brlnoble/RIPT_Capstone/CAD Designs/finger.stl

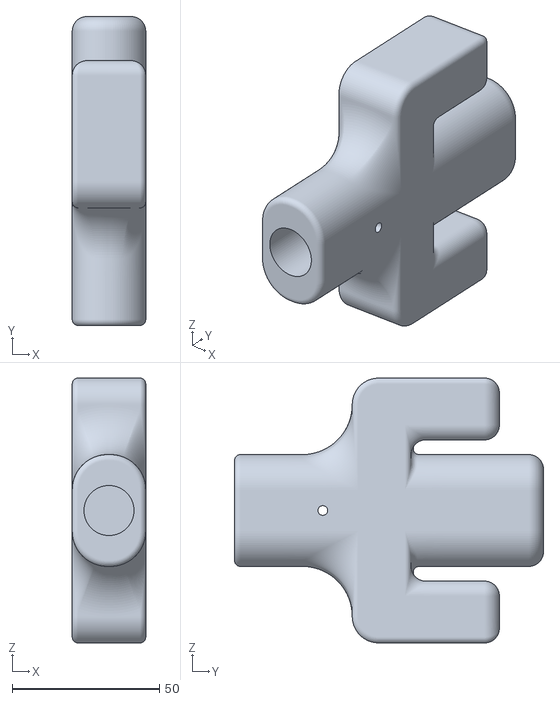
[picture p20: CAD file, 2023-04-15]
CAD Designs/finger.stl
25.0 x 105.0 x 90.0
