brlnoble/RIPT_Capstone/CAD Designs/separator_plate_alternate.stl

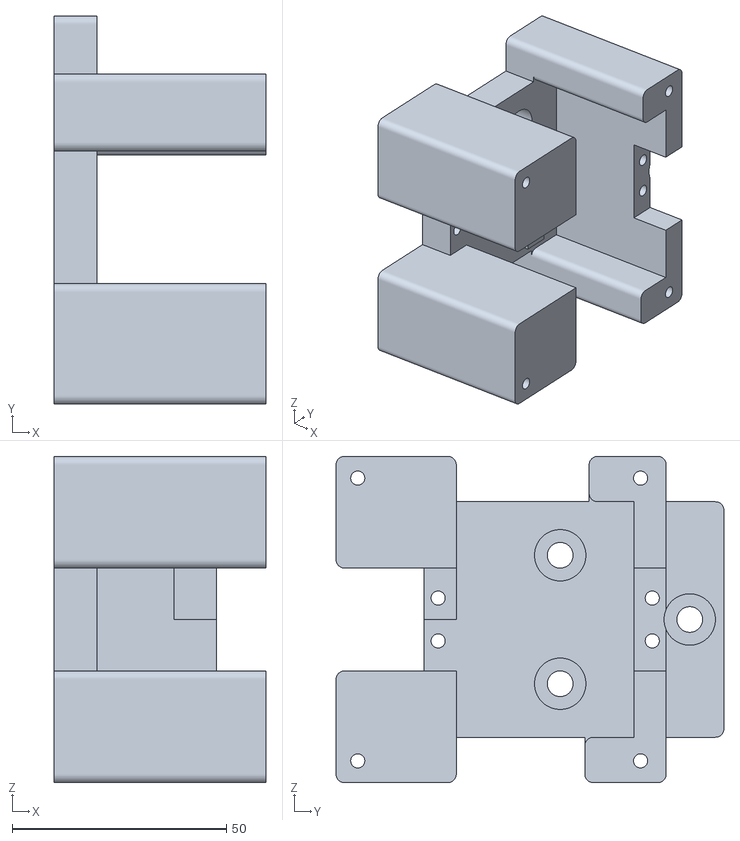
[picture p21: CAD file, 2023-04-15]
CAD Designs/separator_plate_alternate.stl
49.5 x 90.6 x 76.2
