brlnoble/RIPT_Capstone/CAD Designs/servo_horz_plate.stl

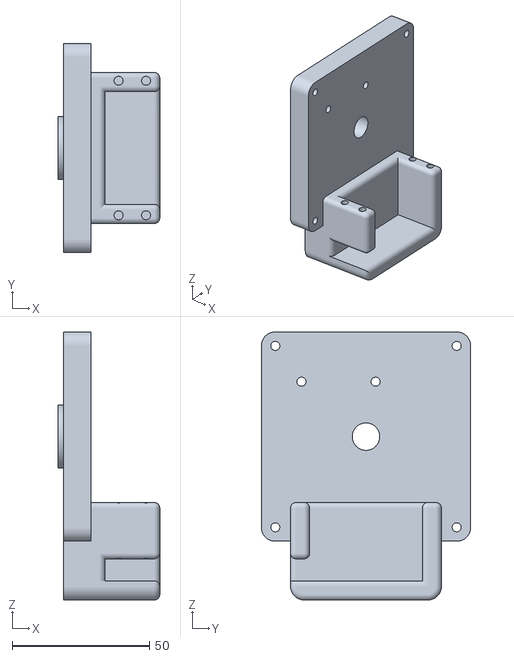
[picture p22: CAD file, 2023-04-15]
CAD Designs/servo_horz_plate.stl
37.0 x 76.2 x 97.6
