brlnoble/RIPT_Capstone/CAD Designs/servo_pressfit_plate.stl

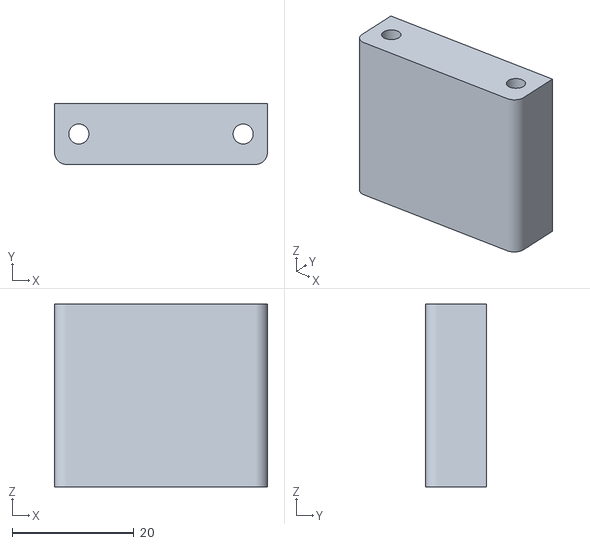
[picture p23: CAD file, 2023-04-15]
CAD Designs/servo_pressfit_plate.stl
35.0 x 10.0 x 30.0
