brlnoble/RIPT_Capstone/CAD Designs/stick_mount.stl

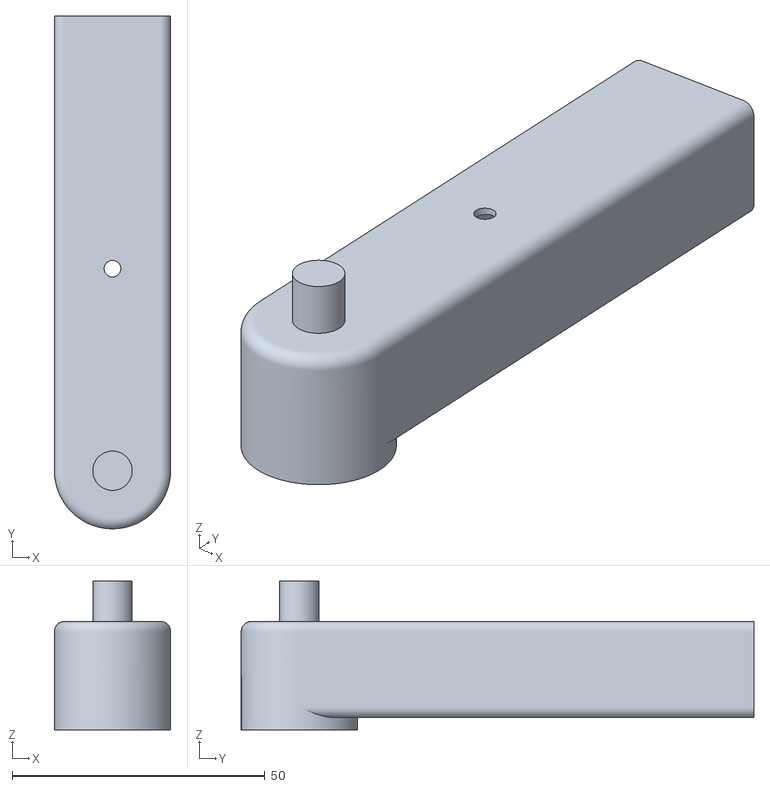
[picture p24: CAD file, 2023-04-15]
CAD Designs/stick_mount.stl
23.0 x 101.5 x 29.5
