brlnoble/RIPT_Capstone/CAD Designs/Slider Top 2.stl

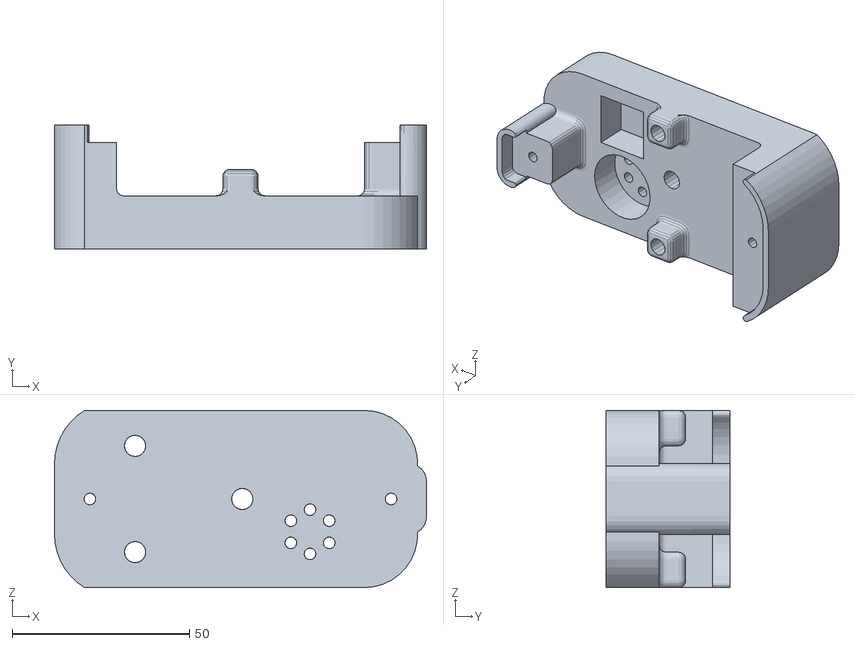
[picture p25: CAD file, 2023-04-15]
CAD Designs/Slider Top 2.stl
105.0 x 35.0 x 50.0
