brlnoble/RIPT_Capstone/MotorMove.py

m1_1 = 1
m1_2 = 2
m2_1 = 3
m2_2 = 4
m1_rx = 5
m1_ry = 6
m2_rx = 7
m2_ry = 8

def MotorMove(x1,x2,y1,y2,type):
    dx=x2-x1
    dy=y2-y1

    xdir = (abs(dx)-dx)/abs(2*dx)
    ydir = (abs(dy)-dy)/abs(2*dy)

def hook():
