brlnoble/RIPT_Capstone/MotorMovementTest.py

import RPi.GPIO as GPIO #for IO control
from time import sleep, perf_counter #for delay functionality
import PySimpleGUI as sg #for simple interface
import random #for random positions

#~~~~~~~~~~~~~~~~~~~~~~~~~~~~~~~~~~~~~~~~~~~~~~~~~~~~~~~~~~~~~~~~~~~~~~~~~~~~~~~~~~~~~~~~~~~~~~~~~
#~~~~~~~~~~~~~~~~~~~~~~~~~~~~~~~~~~~~~~~~~~~~~ Setup ~~~~~~~~~~~~~~~~~~~~~~~~~~~~~~~~~~~~~~~~~~~~~

#Define the stepper motor pins
dirPin1 = 21 #direction pin for motor 1
stepPin1 = 20 #pulse pin for motor 1

dirPin2 = 6 #direction pin for motor 2
stepPin2 = 5 #pulse pin for motor 2

#Define the zeroing pins
zeroPinX = 23
zeroPinY = 24

#Parameters of the motors
speed_max_default =  150e3 #delay between pulses (200k Hz default)
speed_min_default = 75e3
m_delay = 0.5 #delay between movements
m_steps = 1600 #steps per rotation (1/8 microstep)
m_diameter = 1.215 #diameter of the motor gear in cm

#Location tracking
x_location = 0
y_location = 0

#Setup the GPIO pins
GPIO.setmode(GPIO.BCM)

GPIO.setup(dirPin1,GPIO.OUT)
GPIO.setup(stepPin1,GPIO.OUT)
GPIO.setup(dirPin2,GPIO.OUT)
GPIO.setup(stepPin2,GPIO.OUT)

GPIO.setup(zeroPinX,GPIO.IN)
GPIO.setup(zeroPinY,GPIO.OUT)

#Define clockwise and counter clockwise for readability
cw = GPIO.HIGH
ccw = GPIO.LOW

#~~~~~~~~~~~~~~~~~~~~~~~~~~~~~~~~~~~~~~~~~~~~~~~~~~~~~~~~~~~~~~~~~~~~~~~~~~~~~~~~~~~~~~~~~~~~~~~~~
#~~~~~~~~~~~~~~~~~~~~~~~~~~~~~~~~~~~~~~~~~~~ Functions ~~~~~~~~~~~~~~~~~~~~~~~~~~~~~~~~~~~~~~~~~~~

#~~~~~ Convert cm to steps ~~~~~
def Dist_to_Steps(distance):
    return int( (distance / (3.14156 * m_diameter)) * m_steps) #return the number of steps as an integer

#~~~~~ Convert steps to cm ~~~~~
def Steps_to_Dist(steps):
    return (steps / m_steps) * (3.14156 * m_diameter)
    
#~~~~~ Move motors a given number of steps ~~~~~
def Move_Motors(steps,speed_max,speed_min):
    #start_time = perf_counter()
    
    #Accelerate over one rotation if steps and max/min speeds set
    if steps > 1600 and speed_max != speed_min:
        
        accel_step = (speed_max - speed_min)/1600 #Frequency increase per step
        
        for accel in range(0,1600):
            
            accel_speed = 1 / (accel_step*accel + speed_min) #New speed
            
            GPIO.output(stepPin1,GPIO.HIGH)
            GPIO.output(stepPin2,GPIO.HIGH)
            sleep(accel_speed)
            GPIO.output(stepPin1,GPIO.LOW)
            GPIO.output(stepPin2,GPIO.LOW)
            sleep(accel_speed)
            
        #Correct steps and speed for acceleration        
        steps -= 1600
        speed = 1 / speed_max #convert frequency to seconds

    #Move at minimum speed otherwise
    else:
        speed = 1 / speed_min #convert frequency to seconds
    
    #Move the motor in the specified direction for the specified number of steps
    for step in range(steps):
        GPIO.output(stepPin1,GPIO.HIGH)
        GPIO.output(stepPin2,GPIO.HIGH)
        sleep(speed)
        GPIO.output(stepPin1,GPIO.LOW)
        GPIO.output(stepPin2,GPIO.LOW)
        sleep(speed)

#~~~~~ Change motor direction ~~~~~
def Motor_Direction(direction):
    #Change motor direction as specified
    if direction == "up":
        GPIO.output(dirPin1,ccw)
        GPIO.output(dirPin2,cw)
    elif direction == "down":
        GPIO.output(dirPin1,cw)
        GPIO.output(dirPin2,ccw)
    elif direction == "left":
        GPIO.output(dirPin1,ccw)
        GPIO.output(dirPin2,ccw)
    elif direction == "right":
        GPIO.output(dirPin1,cw)
        GPIO.output(dirPin2,cw)

#~~~~~ Movement based on direction and distance ~~~~~
def Move_Distance(direction,distance,x_pos,y_pos):
    start_time = perf_counter()
    #Change motor direction as specified
    Motor_Direction(direction)

    steps_to_move = Dist_to_Steps(distance) #number of steps to move
    dist_to_move = Steps_to_Dist(steps_to_move) #actual distance moved after rounding
    dist_to_move = distance

    #Calculate new position
    if direction == "up":
        y_pos += dist_to_move
        
        #Set the speed for movement
        speed_max = speed_max_default
        speed_min = speed_min_default
        
    elif direction == "down":
        y_pos -= dist_to_move
        
        #Set the speed for movement
        speed_max = speed_max_default
        speed_min = speed_min_default
        
    elif direction == "left":
        x_pos -= dist_to_move
        
        #Set the speed for movement
        speed_max = speed_max_default/2
        speed_min = speed_min_default/2
        
    elif direction == "right":
        x_pos += dist_to_move
        
        #Set the speed for movement
        speed_max = speed_max_default/2
        speed_min = speed_min_default/2

    #Move the motors into position
    if distance != 0:
        Move_Motors(steps_to_move,speed_max,speed_min)
        
        print("\tSteps: " + str(steps_to_move))
        print("\tDist: " + str(dist_to_move))
        print("\tAcc: " + str(100 * (dist_to_move - distance) / distance) + "%")

    end_time = perf_counter()
    print("\tTotal Time: " + str(end_time - start_time) )
    return (x_pos, y_pos) #Return the new X,Y position

#Move to a specific position
def Move_To(x_move,y_move,x_curr,y_curr):
    #Make sure values are valid first
    if x_move <= 12.0 and x_move >= 0.0 and y_move <= 45.0 and y_move >= 0.0:
        
        #Calculate relative movements to get into position
        x_move = x_move - x_curr
        y_move = y_move - y_curr

        x_move_direction = "right" if x_move > 0.0 else "left"
        y_move_direction = "up" if y_move > 0.0 else "down"
        
        #Move Y position first
        x_curr,y_curr = Move_Distance(y_move_direction,abs(y_move),x_curr,y_curr)
        
        sleep(0.5)
        
        #Move X position second
        x_curr,y_curr = Move_Distance(x_move_direction,abs(x_move),x_curr,y_curr)
        
        sleep(0.5)
        
        return x_curr,y_curr
    
    #If invlaid input
    else:
        return x_curr,y_curr
        

#~~~~~ Zero the location (to be used later) ~~~~~
def Zero_Motors():

    #Move the motors slightly in case they are already in the zero position
    Move_Distance("up",2,0,0) #Move up 2cm
    sleep(1)
    Move_Distance("right",2,0,0) #Move right 2cm
    sleep(1)

    #Zero the Y position first
    Motor_Direction("down")
    while(GPIO.input(zeroPinY) == GPIO.HIGH):
        Move_Motors(1,1e3,1e3) #very slowly move motors 1 step at a time

    print("Y has been zeroed...")
    sleep(2)

    #Zero the X position second
    Motor_Direction("left")
    while(GPIO.input(zeroPinX) == GPIO.HIGH):
        Move_Motors(1,1e3,1e3) #very slowly move motors 1 step at a time
        
    print("X has been zeroed...")
    sleep(2)
    #Move the motors slightly off the actual zero point
    Motor_Direction("right")
    for i in range(800):
        Move_Motors(1,10e3,10e3)
    sleep(1)
    Motor_Direction("up")
    for i in range(800):
        Move_Motors(1,10e3,10e3)
    sleep(1)

    return (0,0) #return the new X,Y positon

#~~~~~~~~~~~~~~~~~~~~~~~~~~~~~~~~~~~~~~~~~~~~~~~~~~~~~~~~~~~~~~~~~~~~~~~~~~~~~~~~~~~~~~~~~~~~~~~~~
#~~~~~~~~~~~~~~~~~~~~~~~~~~~~~~~~~~~~~~~~~~~ GUI Setup ~~~~~~~~~~~~~~~~~~~~~~~~~~~~~~~~~~~~~~~~~~~

#Window theme
sg.theme('DefaultNoMoreNagging')
sg.theme_text_element_background_color(color = '#EEE')
sg.theme_text_color('#1D2873')
sg.theme_background_color('#EEE')

font = ('Arial', 16)
btn_font = ('Arial', 16, 'bold')

#Diagram in base 64
hbot = b"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"

#Left side of screen
layout_left = [
    [sg.Text("Input the distance to be moved, and select the direction.",font=font)],
    [sg.Text("Distance in cm: ",font=btn_font),sg.Input("0",key="dist_move",enable_events=True,size=(5,1))],
    [sg.Text()],
    
    [sg.Column(
        [
            [sg.VPush()],
            [sg.Button("Left",key="move_left",font=btn_font,button_color='#02AB29',size=(5,1))],
            [sg.VPush()],
        ],element_justification='c'
    ),

    sg.Column(
        [
            [sg.Button("Up",key="move_up",font=btn_font,button_color='#F5AC11',size=(5,1))],
            [sg.Image(hbot,pad=(0,0))],
            [sg.Button("Down",key="move_down",font=btn_font,button_color='#F5AC11',size=(5,1))],
        ],element_justification='c'
    ),

    sg.Column(
        [
            [sg.VPush()],
            [sg.Button("Right",key="move_right",font=btn_font,button_color='#02AB29',size=(5,1))],
            [sg.VPush()],
        ],element_justification='c'
    )],
]

#Right side
layout_right = [
    [sg.Text("Enter a position to move to in cm.",font=font)],
    [sg.Text("X position (0 - 12): ",font=btn_font),sg.Input("0",key="x_move",font=font,enable_events=True,size=(5,1))],
    [sg.Text("Y position (0 - 45): ",font=btn_font),sg.Input("0",key="y_move",font=font,enable_events=True,size=(5,1))],
    [sg.Text()],
    [sg.Button("Move to Position",key="move_position",font=btn_font,enable_events=True,button_color='#F57627')],
    [sg.Text()],
    [sg.Button("Random Position",key="rand_position",font=btn_font,enable_events=True,button_color='red')],
    [sg.Text()],
    [sg.Text()],
    [sg.Button("Zero Position",key="zero_position",font=btn_font)],
]

#Total layout
layout = [
    [sg.Column(layout_left,element_justification='c'),sg.Column([[]],background_color='#1D2873',expand_y=True),sg.Column(layout_right,element_justification='c')],
    [sg.Text("",font=font,key="info")],
    [sg.Button("Exit",key="close_program_btn",font=btn_font,button_color='#F5273A',size=(10,1))],
]

window = sg.Window('Movement Test',layout,element_justification='c',finalize=True)


#~~~~~~~~~~~~~~~~~~~~~~~~~~~~~~~~~~~~~~~~~~~~~~~~~~~~~~~~~~~~~~~~~~~~~~~~~~~~~~~~~~~~~~~~~~~~~~~~~
#~~~~~~~~~~~~~~~~~~~~~~~~~~~~~~~~~~~~~~~~~~~ Main Loop ~~~~~~~~~~~~~~~~~~~~~~~~~~~~~~~~~~~~~~~~~~~

while True:
    event, values = window.read(timeout=100)

    #If user closes the window
    if event in (sg.WINDOW_CLOSED,"close_program_btn"):
        break

    #Move based a relative distance
    if event in ("move_up","move_down","move_left","move_right"):
        if values["dist_move"] != "":            
            x_location,y_location = Move_Distance(event[5:],float(values["dist_move"]),x_location,y_location) #Move and get new location
            window["info"].update("Position: (" + str(x_location) + ", " + str(y_location) + ")")
            
            window["dist_move"].update(value="0")

    #Move to a specified position
    elif event == "move_position":
        #Make sure values are valid first
        if values["x_move"] != "" and values["y_move"] != "":
            x_move = float(values["x_move"])
            y_move = float(values["y_move"])
            
            x_location,y_location = Move_To(x_move,y_move,x_location,y_location)

            window["info"].update("Position: (" + str(x_location) + ", " + str(y_location) + ")")

            
    elif event == "rand_position":        
        x_move = random.randint(0,8)
        y_move = random.randint(0,35)
        
        x_location,y_location = Move_To(x_move,y_move,x_location,y_location)
        window["info"].update("Position: (" + str(x_location) + ", " + str(y_location) + ")")
        
        
    #Zero the motors
    elif event == "zero_position":
        x_location,y_location = Zero_Motors()
        window["info"].update("Position: (" + str(x_location) + ", " + str(y_location) + ")")

#Program closed, clear everything
window.close()
GPIO.cleanup()
